squiggles1024/KeyPad/KeyPad_Project/ECAD/B4B-PH-SM4-TB/B4B-PH-SM4-TB.step

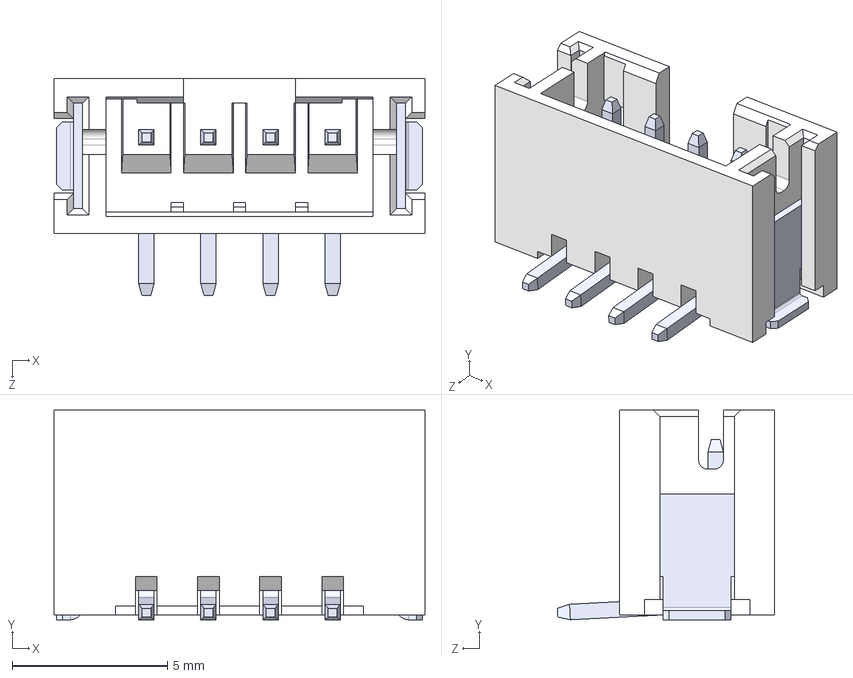
[picture p24: CAD file, 2022-12-01]
KeyPad_Project/ECAD/B4B-PH-SM4-TB/B4B-PH-SM4-TB.step
12.0 x 6.75 x 7.00 mm
