squiggles1024/KeyPad/KeyPad_Project/ECAD/JS5208/JS5208.step

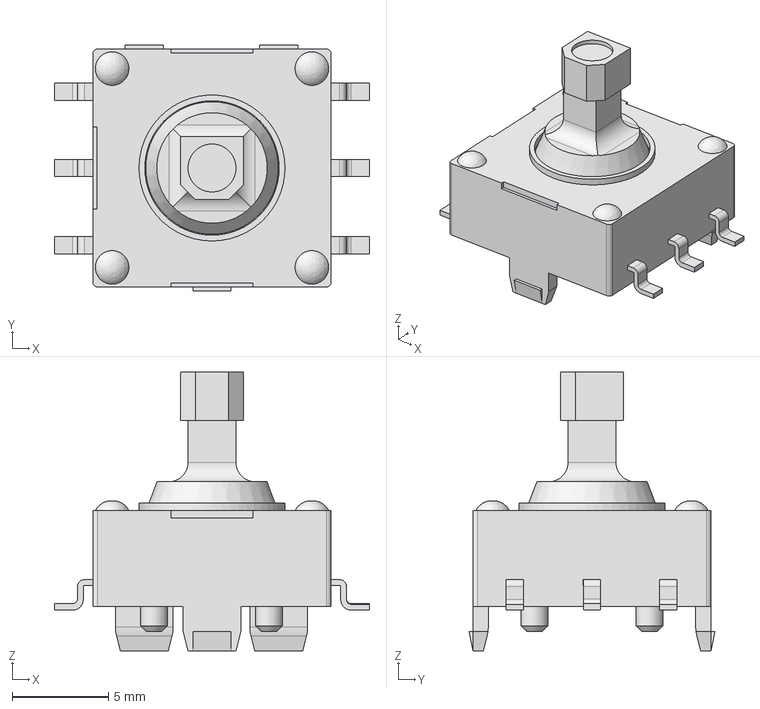
[picture p25: CAD file, 2022-12-01]
KeyPad_Project/ECAD/JS5208/JS5208.step
16.4 x 12.8 x 14.5 mm
