squiggles1024/KeyPad/KeyPad_Project/CAD Parts/12mm-button-without-cap-with-round-square-cap-1.snapshot.3/12mmx12mm With White cap square.stp

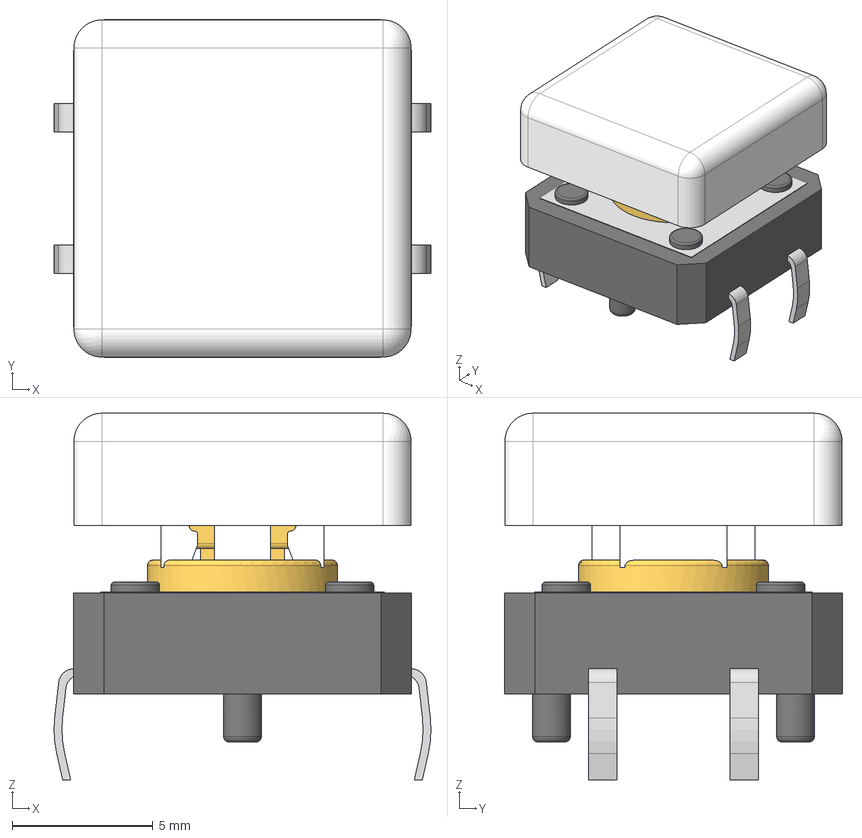
[picture p26: CAD file, 2022-12-01]
KeyPad_Project/CAD Parts/12mm-button-without-cap-with-round-square-cap-1.snapshot.3/12mmx12mm With White cap square.stp
13.4 x 12.0 x 13.0 mm
