squiggles1024/KeyPad/KeyPad_Project/CAD Parts/WheelCover.SLDPRT

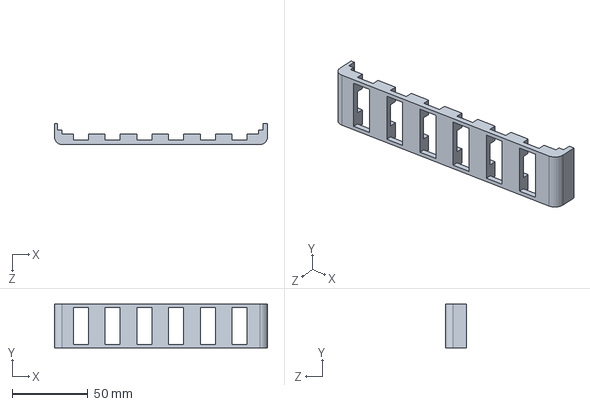
[picture p29: CAD file, 2022-12-01]
KeyPad_Project/CAD Parts/WheelCover.SLDPRT
141.0 x 28.8 x 14.0 mm
