squiggles1024/KeyPad/KeyPad_Project/CAD Parts/d-sub-connector-femaile-1.snapshot.1/femaile/db15.stp

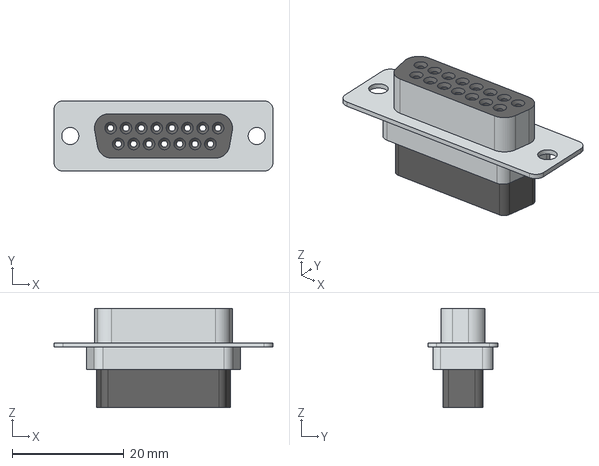
[picture p30: CAD file, 2022-12-01]
KeyPad_Project/CAD Parts/d-sub-connector-femaile-1.snapshot.1/femaile/db15.stp
39.1 x 12.5 x 17.7 mm
