squiggles1024/KeyPad/KeyPad_Project/CAD Parts/tactile-switch-thru-6mm-series-1.snapshot.25/Tactal Switch -Thru (6mmx 6mmx17.0mm).stp

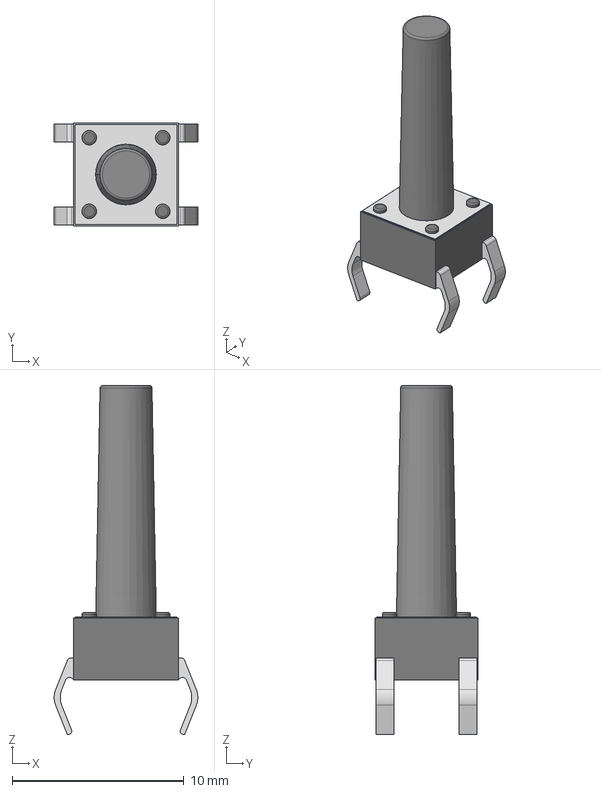
[picture p31: CAD file, 2022-12-01]
KeyPad_Project/CAD Parts/tactile-switch-thru-6mm-series-1.snapshot.25/Tactal Switch -Thru (6mmx 6mmx17.0mm).stp
8.37 x 5.99 x 20.3 mm
