squiggles1024/KeyPad/KeyPad_Project/CAD Parts/BoardCover.SLDPRT

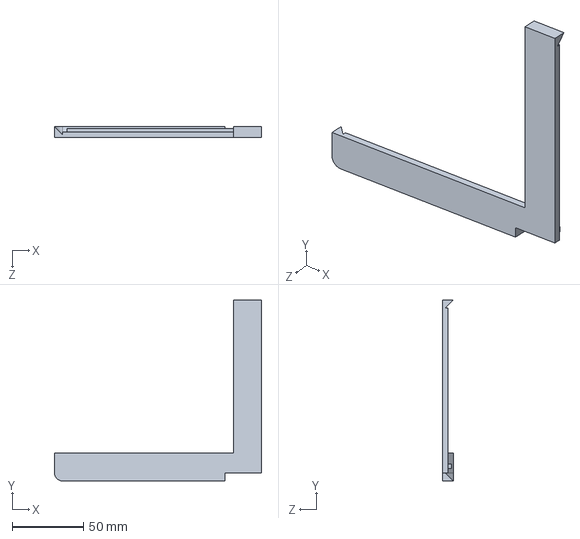
[picture p33: CAD file, 2022-12-01]
KeyPad_Project/CAD Parts/BoardCover.SLDPRT
145.7 x 127.3 x 7.66 mm
