squiggles1024/KeyPad/KeyPad_Project/CAD Parts/ThumbpadBase.SLDPRT

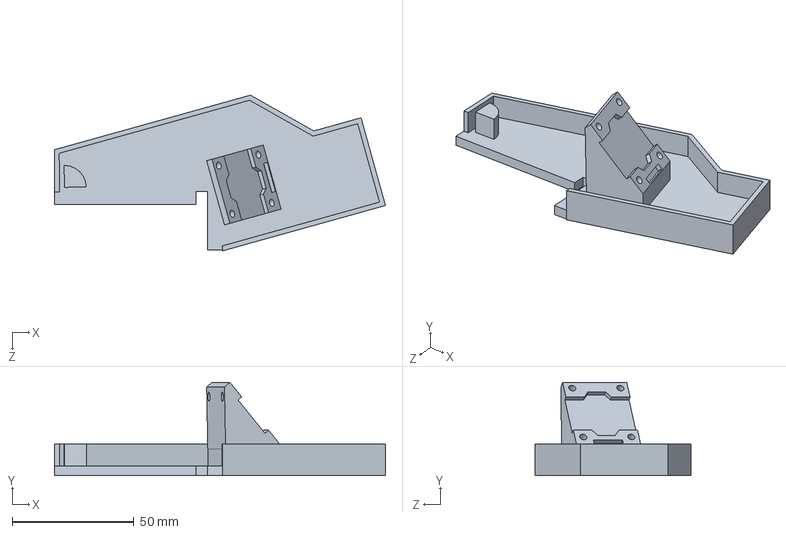
[picture p37: CAD file, 2022-12-01]
KeyPad_Project/CAD Parts/ThumbpadBase.SLDPRT
136.0 x 38.4 x 64.0 mm
