squiggles1024/KeyPad/KeyPad_Project/CAD Parts/tactile-switch-thru-6mm-series-1.snapshot.25/Tactal Switch -Thru (6mmx 6mmx4.5mm).stp

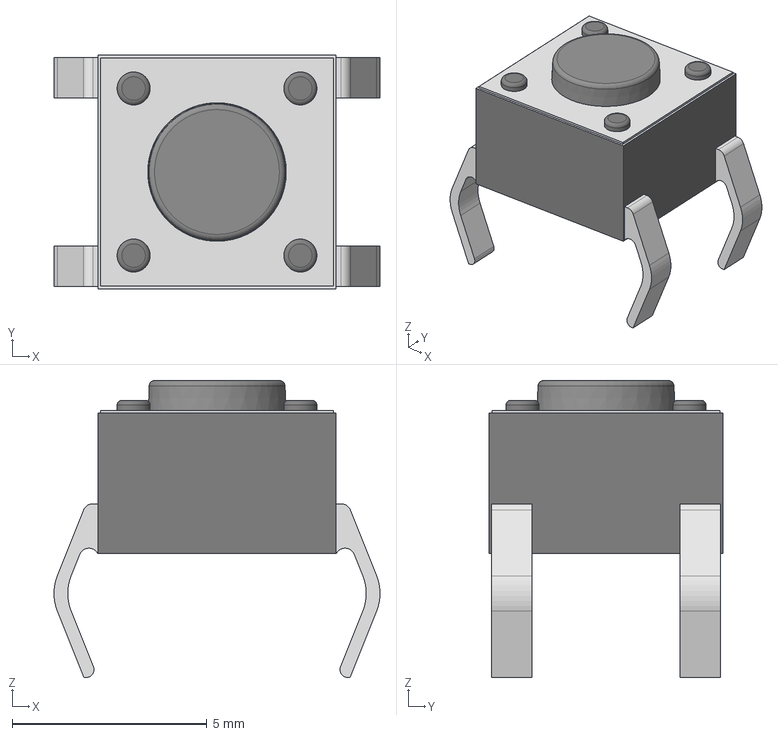
[picture p38: CAD file, 2022-12-01]
KeyPad_Project/CAD Parts/tactile-switch-thru-6mm-series-1.snapshot.25/Tactal Switch -Thru (6mmx 6mmx4.5mm).stp
8.37 x 5.99 x 7.62 mm
