squiggles1024/KeyPad/KeyPad_Project/CAD Parts/Housing.SLDPRT

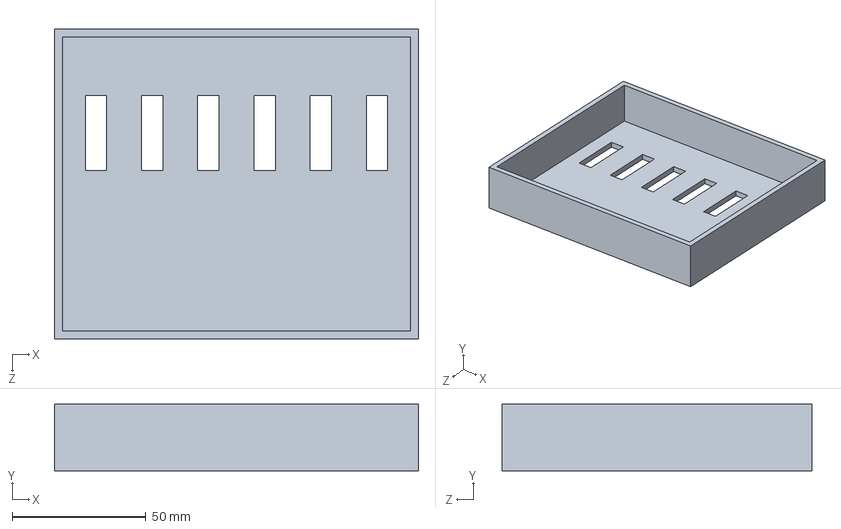
[picture p39: CAD file, 2022-12-01]
KeyPad_Project/CAD Parts/Housing.SLDPRT
136.0 x 25.0 x 116.0 mm
