squiggles1024/KeyPad/KeyPad_Project/CAD Parts/KeypadBase.SLDPRT

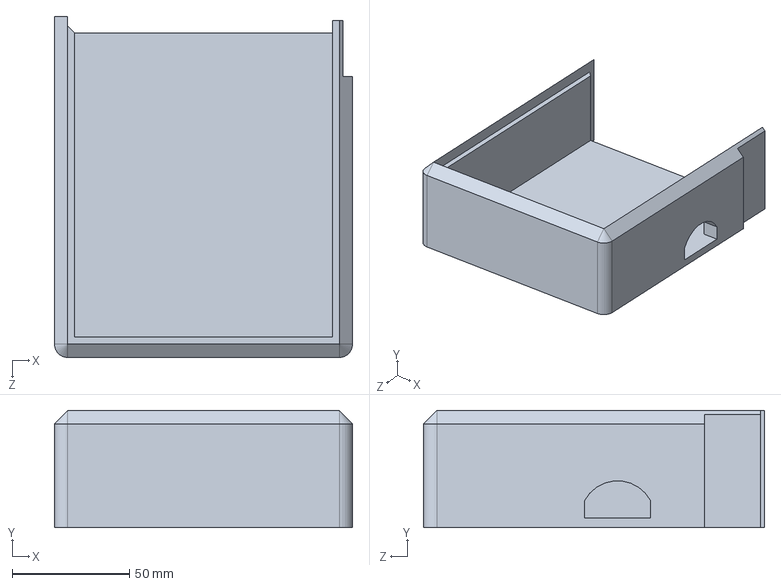
[picture p42: CAD file, 2022-12-01]
KeyPad_Project/CAD Parts/KeypadBase.SLDPRT
127.3 x 50.0 x 145.7 mm
