squiggles1024/KeyPad/KeyPad_Project/CAD Parts/WheelBracket.SLDPRT

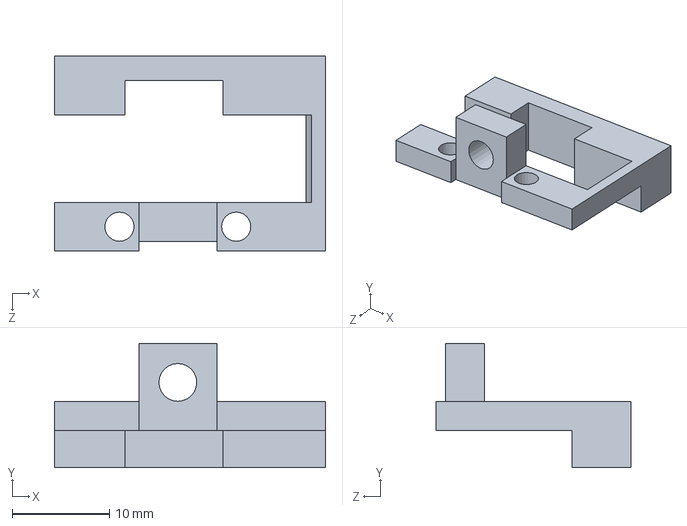
[picture p45: CAD file, 2022-12-01]
KeyPad_Project/CAD Parts/WheelBracket.SLDPRT
27.9 x 12.7 x 20.0 mm
