squiggles1024/KeyPad/KeyPad_Project/CAD Parts/Sensei Scroll Wheel.3MF

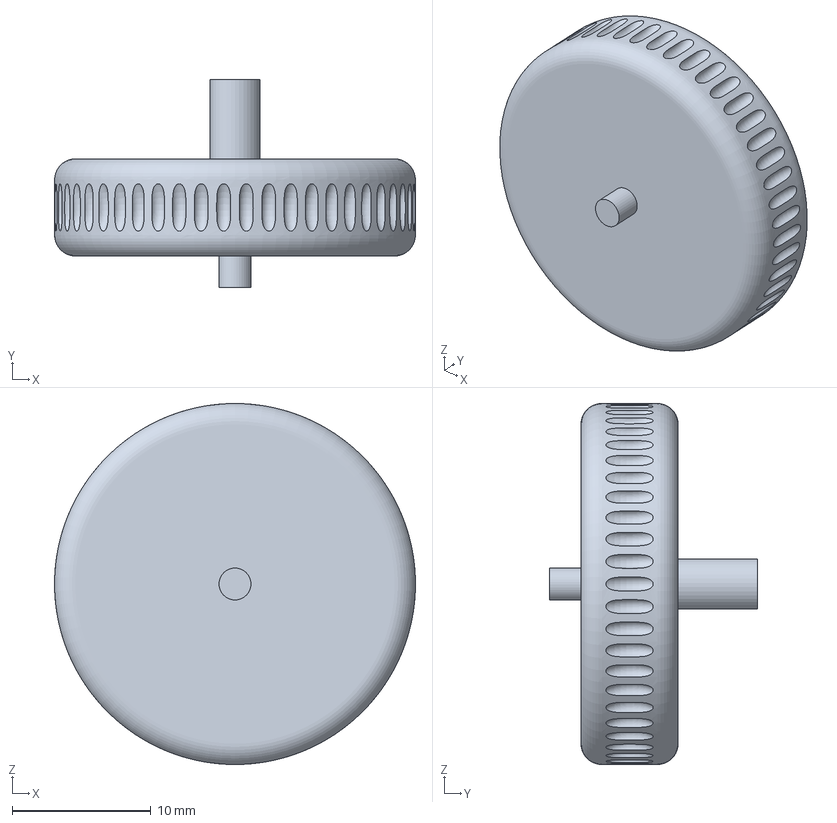
[picture p46: CAD file, 2022-12-01]
KeyPad_Project/CAD Parts/Sensei Scroll Wheel.3MF
26.0 x 14.9 x 26.0 mm
