squiggles1024/KeyPad/KeyPad_Project/CAD Parts/Rim.SLDPRT

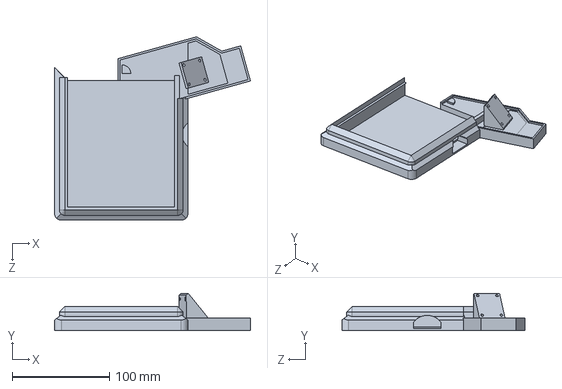
[picture p48: CAD file, 2022-12-01]
KeyPad_Project/CAD Parts/Rim.SLDPRT
201.5 x 38.4 x 188.5 mm
