squiggles1024/KeyPad/KeyPad_Project/CAD Parts/Thumbpad.SLDPRT

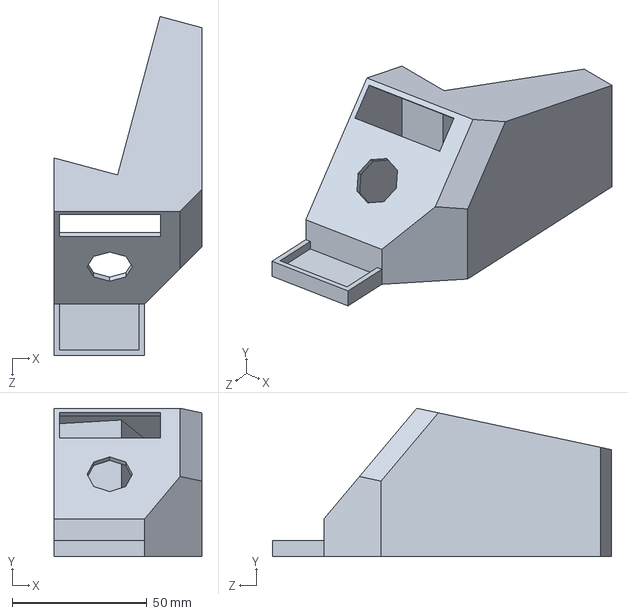
[picture p52: CAD file, 2022-12-01]
KeyPad_Project/CAD Parts/Thumbpad.SLDPRT
54.6 x 55.0 x 125.6 mm
