squiggles1024/KeyPad/KeyPad_Project/CAD Parts/TouchScreenHolder.SLDPRT

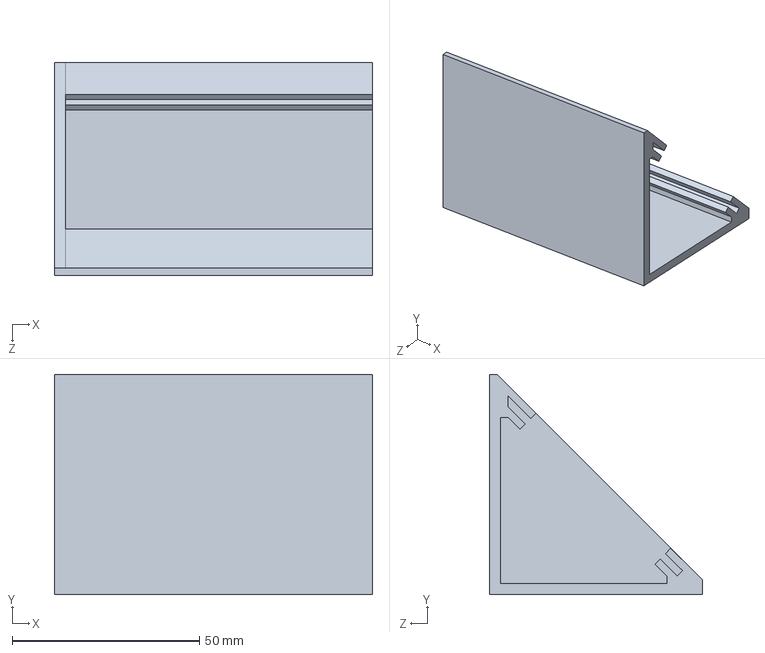
[picture p54: CAD file, 2022-12-01]
KeyPad_Project/CAD Parts/TouchScreenHolder.SLDPRT
85.0 x 58.9 x 57.0 mm
