squiggles1024/KeyPad/KeyPad_Project/CAD Parts/HandRest2.SLDPRT

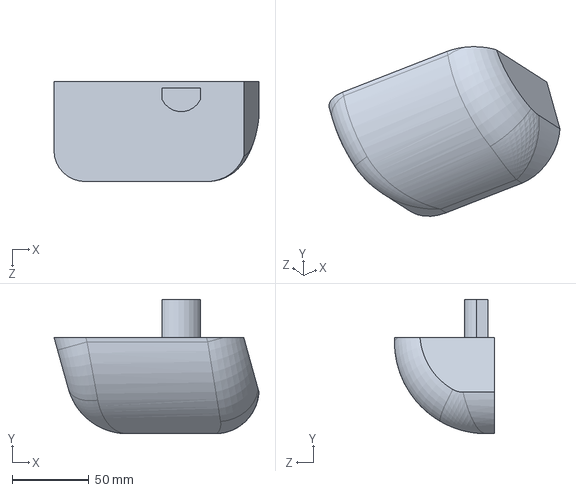
[picture p55: CAD file, 2022-12-01]
KeyPad_Project/CAD Parts/HandRest2.SLDPRT
133.9 x 87.9 x 65.5 mm
