squiggles1024/KeyPad/KeyPad_Project/CAD Parts/KeyCap.SLDPRT

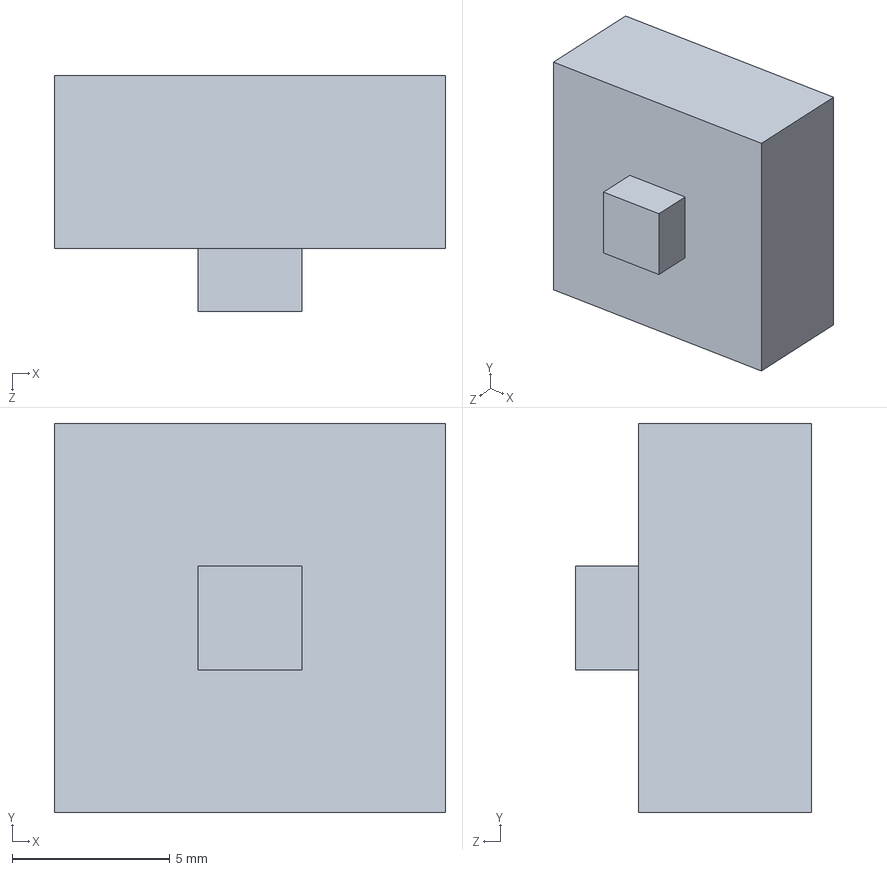
[picture p57: CAD file, 2022-12-01]
KeyPad_Project/CAD Parts/KeyCap.SLDPRT
12.4 x 12.4 x 7.50 mm
