squiggles1024/KeyPad/Core/Inc/main.h

#define ADC_VX_Pin GPIO_PIN_3
#define ADC_VX_GPIO_Port GPIOA
#define ADC_VY_Pin GPIO_PIN_4
#define ADC_VY_GPIO_Port GPIOA
#define SPI1_CSN_Pin GPIO_PIN_0
#define SPI1_CSN_GPIO_Port GPIOB
#define DCRS_Pin GPIO_PIN_1
#define DCRS_GPIO_Port GPIOB
