squiggles1024/KeyPad/Core/Src/i2c.c

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
/* Includes ------------------------------------------------------------------*/
#include "i2c.h"

I2C_HandleTypeDef hi2c1;
I2C_HandleTypeDef hi2c2;
DMA_HandleTypeDef hdma_i2c1_rx;
DMA_HandleTypeDef hdma_i2c2_rx;

/* I2C1 init function */
void MX_I2C1_Init(void)
{

  hi2c1.Instance = I2C1;
  hi2c1.Init.ClockSpeed = 400000;
  hi2c1.Init.DutyCycle = I2C_DUTYCYCLE_2;
  hi2c1.Init.OwnAddress1 = 0;
  hi2c1.Init.AddressingMode = I2C_ADDRESSINGMODE_7BIT;
  hi2c1.Init.DualAddressMode = I2C_DUALADDRESS_DISABLE;
  hi2c1.Init.OwnAddress2 = 0;
  hi2c1.Init.GeneralCallMode = I2C_GENERALCALL_DISABLE;
  hi2c1.Init.NoStretchMode = I2C_NOSTRETCH_DISABLE;
  if (HAL_I2C_Init(&hi2c1) != HAL_OK)
  {
    Error_Handler();
  }
}
/* I2C2 init function */
void MX_I2C2_Init(void)
{

  hi2c2.Instance = I2C2;
  hi2c2.Init.ClockSpeed = 100000;
  hi2c2.Init.DutyCycle = I2C_DUTYCYCLE_2;
  hi2c2.Init.OwnAddress1 = 0;
  hi2c2.Init.AddressingMode = I2C_ADDRESSINGMODE_7BIT;
  hi2c2.Init.DualAddressMode = I2C_DUALADDRESS_DISABLE;
  hi2c2.Init.OwnAddress2 = 0;
  hi2c2.Init.GeneralCallMode = I2C_GENERALCALL_DISABLE;
  hi2c2.Init.NoStretchMode = I2C_NOSTRETCH_DISABLE;
  if (HAL_I2C_Init(&hi2c2) != HAL_OK)
  {
    Error_Handler();
  }
}

void HAL_I2C_MspInit(I2C_HandleTypeDef* i2cHandle)
{

  GPIO_InitTypeDef GPIO_InitStruct = {0};
  if(i2cHandle->Instance==I2C1)
  {
    __HAL_RCC_GPIOB_CLK_ENABLE();
    /**I2C1 GPIO Configuration
    PB6     ------> I2C1_SCL
    PB7     ------> I2C1_SDA
    */
    GPIO_InitStruct.Pin = GPIO_PIN_6|GPIO_PIN_7;
    GPIO_InitStruct.Mode = GPIO_MODE_AF_OD;
    GPIO_InitStruct.Pull = GPIO_PULLUP;
    GPIO_InitStruct.Speed = GPIO_SPEED_FREQ_VERY_HIGH;
    GPIO_InitStruct.Alternate = GPIO_AF4_I2C1;
    HAL_GPIO_Init(GPIOB, &GPIO_InitStruct);

    /* I2C1 clock enable */
    __HAL_RCC_I2C1_CLK_ENABLE();

    /* I2C1 DMA Init */
    /* I2C1_RX Init */
    hdma_i2c1_rx.Instance = DMA1_Stream0;
    hdma_i2c1_rx.Init.Channel = DMA_CHANNEL_1;
    hdma_i2c1_rx.Init.Direction = DMA_PERIPH_TO_MEMORY;
    hdma_i2c1_rx.Init.PeriphInc = DMA_PINC_DISABLE;
    hdma_i2c1_rx.Init.MemInc = DMA_MINC_ENABLE;
    hdma_i2c1_rx.Init.PeriphDataAlignment = DMA_PDATAALIGN_BYTE;
    hdma_i2c1_rx.Init.MemDataAlignment = DMA_MDATAALIGN_BYTE;
    hdma_i2c1_rx.Init.Mode = DMA_NORMAL;
    hdma_i2c1_rx.Init.Priority = DMA_PRIORITY_LOW;
    hdma_i2c1_rx.Init.FIFOMode = DMA_FIFOMODE_DISABLE;
    if (HAL_DMA_Init(&hdma_i2c1_rx) != HAL_OK)
    {
      Error_Handler();
    }

    __HAL_LINKDMA(i2cHandle,hdmarx,hdma_i2c1_rx);

  }
  else if(i2cHandle->Instance==I2C2)
  {
    __HAL_RCC_GPIOB_CLK_ENABLE();
    /**I2C2 GPIO Configuration
    PB10     ------> I2C2_SCL
    PB3     ------> I2C2_SDA
    */
    GPIO_InitStruct.Pin = GPIO_PIN_10;
    GPIO_InitStruct.Mode = GPIO_MODE_AF_OD;
    GPIO_InitStruct.Pull = GPIO_NOPULL;
    GPIO_InitStruct.Speed = GPIO_SPEED_FREQ_VERY_HIGH;
    GPIO_InitStruct.Alternate = GPIO_AF4_I2C2;
    HAL_GPIO_Init(GPIOB, &GPIO_InitStruct);

    GPIO_InitStruct.Pin = GPIO_PIN_3;
    GPIO_InitStruct.Mode = GPIO_MODE_AF_OD;
    GPIO_InitStruct.Pull = GPIO_NOPULL;
    GPIO_InitStruct.Speed = GPIO_SPEED_FREQ_VERY_HIGH;
    GPIO_InitStruct.Alternate = GPIO_AF9_I2C2;
    HAL_GPIO_Init(GPIOB, &GPIO_InitStruct);

    /* I2C2 clock enable */
    __HAL_RCC_I2C2_CLK_ENABLE();

    /* I2C2 DMA Init */
    /* I2C2_RX Init */
    hdma_i2c2_rx.Instance = DMA1_Stream2;
    hdma_i2c2_rx.Init.Channel = DMA_CHANNEL_7;
    hdma_i2c2_rx.Init.Direction = DMA_PERIPH_TO_MEMORY;
    hdma_i2c2_rx.Init.PeriphInc = DMA_PINC_DISABLE;
    hdma_i2c2_rx.Init.MemInc = DMA_MINC_ENABLE;
    hdma_i2c2_rx.Init.PeriphDataAlignment = DMA_PDATAALIGN_BYTE;
    hdma_i2c2_rx.Init.MemDataAlignment = DMA_MDATAALIGN_BYTE;
    hdma_i2c2_rx.Init.Mode = DMA_NORMAL;
    hdma_i2c2_rx.Init.Priority = DMA_PRIORITY_LOW;
    hdma_i2c2_rx.Init.FIFOMode = DMA_FIFOMODE_DISABLE;
    if (HAL_DMA_Init(&hdma_i2c2_rx) != HAL_OK)
    {
      Error_Handler();
    }

    __HAL_LINKDMA(i2cHandle,hdmarx,hdma_i2c2_rx);

  }
}

void HAL_I2C_MspDeInit(I2C_HandleTypeDef* i2cHandle)
{

  if(i2cHandle->Instance==I2C1)
  {
    /* Peripheral clock disable */
    __HAL_RCC_I2C1_CLK_DISABLE();

    /**I2C1 GPIO Configuration
    PB6     ------> I2C1_SCL
    PB7     ------> I2C1_SDA
    */
    HAL_GPIO_DeInit(GPIOB, GPIO_PIN_6);

    HAL_GPIO_DeInit(GPIOB, GPIO_PIN_7);

    /* I2C1 DMA DeInit */
    HAL_DMA_DeInit(i2cHandle->hdmarx);
  }
  else if(i2cHandle->Instance==I2C2)
  {
    /* Peripheral clock disable */
    __HAL_RCC_I2C2_CLK_DISABLE();

    /**I2C2 GPIO Configuration
    PB10     ------> I2C2_SCL
    PB3     ------> I2C2_SDA
    */
    HAL_GPIO_DeInit(GPIOB, GPIO_PIN_10);

    HAL_GPIO_DeInit(GPIOB, GPIO_PIN_3);

    /* I2C2 DMA DeInit */
    HAL_DMA_DeInit(i2cHandle->hdmarx);
  }
}

/* USER CODE BEGIN 1 */
void I2C1_Init(void){

	  hi2c1.Instance = I2C1;
	  hi2c1.Init.ClockSpeed = 400000;
	  hi2c1.Init.DutyCycle = I2C_DUTYCYCLE_2;
	  hi2c1.Init.OwnAddress1 = 0;
	  hi2c1.Init.AddressingMode = I2C_ADDRESSINGMODE_7BIT;
	  hi2c1.Init.DualAddressMode = I2C_DUALADDRESS_DISABLE;
	  hi2c1.Init.OwnAddress2 = 0;
	  hi2c1.Init.GeneralCallMode = I2C_GENERALCALL_DISABLE;
	  hi2c1.Init.NoStretchMode = I2C_NOSTRETCH_DISABLE;
	  if (HAL_I2C_Init(&hi2c1) != HAL_OK)
	  {
	    Error_Handler();
	  }

}

void I2C2_Init(void){
	  hi2c2.Instance = I2C2;
	  hi2c2.Init.ClockSpeed = 100000;
	  hi2c2.Init.DutyCycle = I2C_DUTYCYCLE_2;
	  hi2c2.Init.OwnAddress1 = 0;
	  hi2c2.Init.AddressingMode = I2C_ADDRESSINGMODE_7BIT;
	  hi2c2.Init.DualAddressMode = I2C_DUALADDRESS_DISABLE;
	  hi2c2.Init.OwnAddress2 = 0;
	  hi2c2.Init.GeneralCallMode = I2C_GENERALCALL_DISABLE;
	  hi2c2.Init.NoStretchMode = I2C_NOSTRETCH_DISABLE;
	  if (HAL_I2C_Init(&hi2c2) != HAL_OK)
	  {
	    Error_Handler();
	  }
}
/* USER CODE END 1 */
