squiggles1024/KeyPad/Core/Src/tim.c

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
/* Includes ------------------------------------------------------------------*/
#include "tim.h"

TIM_HandleTypeDef htim3;
DMA_HandleTypeDef hdma_tim3_ch1_trig;

/* TIM3 init function */
void MX_TIM3_Init(void)
{

  TIM_ClockConfigTypeDef sClockSourceConfig = {0};
  TIM_MasterConfigTypeDef sMasterConfig = {0};
  TIM_OC_InitTypeDef sConfigOC = {0};

  htim3.Instance = TIM3;
  htim3.Init.Prescaler = 0;
  htim3.Init.CounterMode = TIM_COUNTERMODE_UP;
  htim3.Init.Period = 168 - 1;
  htim3.Init.ClockDivision = TIM_CLOCKDIVISION_DIV1;
  htim3.Init.AutoReloadPreload = TIM_AUTORELOAD_PRELOAD_ENABLE;
  if (HAL_TIM_Base_Init(&htim3) != HAL_OK)
  {
    Error_Handler();
  }
  sClockSourceConfig.ClockSource = TIM_CLOCKSOURCE_INTERNAL;
  if (HAL_TIM_ConfigClockSource(&htim3, &sClockSourceConfig) != HAL_OK)
  {
    Error_Handler();
  }
  if (HAL_TIM_PWM_Init(&htim3) != HAL_OK)
  {
    Error_Handler();
  }
  sMasterConfig.MasterOutputTrigger = TIM_TRGO_RESET;
  sMasterConfig.MasterSlaveMode = TIM_MASTERSLAVEMODE_DISABLE;
  if (HAL_TIMEx_MasterConfigSynchronization(&htim3, &sMasterConfig) != HAL_OK)
  {
    Error_Handler();
  }
  sConfigOC.OCMode = TIM_OCMODE_PWM1;
  sConfigOC.Pulse = 0;
  sConfigOC.OCPolarity = TIM_OCPOLARITY_HIGH;
  sConfigOC.OCFastMode = TIM_OCFAST_DISABLE;
  if (HAL_TIM_PWM_ConfigChannel(&htim3, &sConfigOC, TIM_CHANNEL_1) != HAL_OK)
  {
    Error_Handler();
  }
  HAL_TIM_MspPostInit(&htim3);

}

void HAL_TIM_Base_MspInit(TIM_HandleTypeDef* tim_baseHandle)
{

  if(tim_baseHandle->Instance==TIM3)
  {
    /* TIM3 clock enable */
    __HAL_RCC_TIM3_CLK_ENABLE();

    /* TIM3 DMA Init */
    /* TIM3_CH1_TRIG Init */
    hdma_tim3_ch1_trig.Instance = DMA1_Stream4;
    hdma_tim3_ch1_trig.Init.Channel = DMA_CHANNEL_5;
    hdma_tim3_ch1_trig.Init.Direction = DMA_MEMORY_TO_PERIPH;
    hdma_tim3_ch1_trig.Init.PeriphInc = DMA_PINC_DISABLE;
    hdma_tim3_ch1_trig.Init.MemInc = DMA_MINC_ENABLE;
    hdma_tim3_ch1_trig.Init.PeriphDataAlignment = DMA_PDATAALIGN_HALFWORD;
    hdma_tim3_ch1_trig.Init.MemDataAlignment = DMA_MDATAALIGN_HALFWORD;
    hdma_tim3_ch1_trig.Init.Mode = DMA_CIRCULAR;
    hdma_tim3_ch1_trig.Init.Priority = DMA_PRIORITY_LOW;
    hdma_tim3_ch1_trig.Init.FIFOMode = DMA_FIFOMODE_DISABLE;
    if (HAL_DMA_Init(&hdma_tim3_ch1_trig) != HAL_OK)
    {
      Error_Handler();
    }

    /* Several peripheral DMA handle pointers point to the same DMA handle.
     Be aware that there is only one stream to perform all the requested DMAs. */
    __HAL_LINKDMA(tim_baseHandle,hdma[TIM_DMA_ID_CC1],hdma_tim3_ch1_trig);
    __HAL_LINKDMA(tim_baseHandle,hdma[TIM_DMA_ID_TRIGGER],hdma_tim3_ch1_trig);

  }
}
void HAL_TIM_MspPostInit(TIM_HandleTypeDef* timHandle)
{

  GPIO_InitTypeDef GPIO_InitStruct = {0};
  if(timHandle->Instance==TIM3)
  {
    __HAL_RCC_GPIOB_CLK_ENABLE();
    /**TIM3 GPIO Configuration
    PB4     ------> TIM3_CH1
    */
    GPIO_InitStruct.Pin = GPIO_PIN_4;
    GPIO_InitStruct.Mode = GPIO_MODE_AF_PP;
    GPIO_InitStruct.Pull = GPIO_NOPULL;
    GPIO_InitStruct.Speed = GPIO_SPEED_FREQ_VERY_HIGH;
    GPIO_InitStruct.Alternate = GPIO_AF2_TIM3;
    HAL_GPIO_Init(GPIOB, &GPIO_InitStruct);

  }

}

void HAL_TIM_Base_MspDeInit(TIM_HandleTypeDef* tim_baseHandle)
{

  if(tim_baseHandle->Instance==TIM3)
  {
    /* Peripheral clock disable */
    __HAL_RCC_TIM3_CLK_DISABLE();

    /* TIM3 DMA DeInit */
    HAL_DMA_DeInit(tim_baseHandle->hdma[TIM_DMA_ID_CC1]);
    HAL_DMA_DeInit(tim_baseHandle->hdma[TIM_DMA_ID_TRIGGER]);
  }
}

/* USER CODE BEGIN 1 */
void TIM3_Init(void){

	  TIM_ClockConfigTypeDef sClockSourceConfig = {0};
	  TIM_MasterConfigTypeDef sMasterConfig = {0};
	  TIM_OC_InitTypeDef sConfigOC = {0};


	  htim3.Instance = TIM3;
	  htim3.Init.Prescaler = 0;
	  htim3.Init.CounterMode = TIM_COUNTERMODE_UP;
	  htim3.Init.Period = 120 - 1;
	  htim3.Init.ClockDivision = TIM_CLOCKDIVISION_DIV1;
	  htim3.Init.AutoReloadPreload = TIM_AUTORELOAD_PRELOAD_DISABLE;
	  if (HAL_TIM_Base_Init(&htim3) != HAL_OK)
	  {
	    Error_Handler();
	  }
	  sClockSourceConfig.ClockSource = TIM_CLOCKSOURCE_INTERNAL;
	  if (HAL_TIM_ConfigClockSource(&htim3, &sClockSourceConfig) != HAL_OK)
	  {
	    Error_Handler();
	  }
	  if (HAL_TIM_PWM_Init(&htim3) != HAL_OK)
	  {
	    Error_Handler();
	  }
	  sMasterConfig.MasterOutputTrigger = TIM_TRGO_RESET;
	  sMasterConfig.MasterSlaveMode = TIM_MASTERSLAVEMODE_DISABLE;
	  if (HAL_TIMEx_MasterConfigSynchronization(&htim3, &sMasterConfig) != HAL_OK)
	  {
	    Error_Handler();
	  }
	  sConfigOC.OCMode = TIM_OCMODE_PWM1;
	  sConfigOC.Pulse = 0;
	  sConfigOC.OCPolarity = TIM_OCPOLARITY_HIGH;
	  sConfigOC.OCFastMode = TIM_OCFAST_DISABLE;
	  if (HAL_TIM_PWM_ConfigChannel(&htim3, &sConfigOC, TIM_CHANNEL_1) != HAL_OK)
	  {
	    Error_Handler();
	  }

	  HAL_TIM_MspPostInit(&htim3);
}

void TIM3_Init2(){

	  TIM_ClockConfigTypeDef sClockSourceConfig = {0};
	  TIM_MasterConfigTypeDef sMasterConfig = {0};
	  TIM_OC_InitTypeDef sConfigOC = {0};

	  htim3.Instance = TIM3;
	  htim3.Init.Prescaler = 0;
	  htim3.Init.CounterMode = TIM_COUNTERMODE_UP;
	  htim3.Init.Period = 168 - 1;
	  htim3.Init.ClockDivision = TIM_CLOCKDIVISION_DIV1;
	  htim3.Init.AutoReloadPreload = TIM_AUTORELOAD_PRELOAD_ENABLE;
	  if (HAL_TIM_Base_Init(&htim3) != HAL_OK)
	  {
	    Error_Handler();
	  }
	  sClockSourceConfig.ClockSource = TIM_CLOCKSOURCE_INTERNAL;
	  if (HAL_TIM_ConfigClockSource(&htim3, &sClockSourceConfig) != HAL_OK)
	  {
	    Error_Handler();
	  }
	  if (HAL_TIM_PWM_Init(&htim3) != HAL_OK)
	  {
	    Error_Handler();
	  }
	  sMasterConfig.MasterOutputTrigger = TIM_TRGO_RESET;
	  sMasterConfig.MasterSlaveMode = TIM_MASTERSLAVEMODE_DISABLE;
	  if (HAL_TIMEx_MasterConfigSynchronization(&htim3, &sMasterConfig) != HAL_OK)
	  {
	    Error_Handler();
	  }
	  sConfigOC.OCMode = TIM_OCMODE_PWM1;
	  sConfigOC.Pulse = 0;
	  sConfigOC.OCPolarity = TIM_OCPOLARITY_HIGH;
	  sConfigOC.OCFastMode = TIM_OCFAST_DISABLE;
	  if (HAL_TIM_PWM_ConfigChannel(&htim3, &sConfigOC, TIM_CHANNEL_1) != HAL_OK)
	  {
	    Error_Handler();
	  }
	  HAL_TIM_MspPostInit(&htim3);

}
/* USER CODE END 1 */
