squiggles1024/KeyPad/Core/Src/adc.c

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
/* Includes ------------------------------------------------------------------*/
#include "adc.h"

ADC_HandleTypeDef hadc1;
DMA_HandleTypeDef hdma_adc1;

/* ADC1 init function */
void MX_ADC1_Init(void)
{

  ADC_ChannelConfTypeDef sConfig = {0};

  /** Configure the global features of the ADC (Clock, Resolution, Data Alignment and number of conversion)
  */
  hadc1.Instance = ADC1;
  hadc1.Init.ClockPrescaler = ADC_CLOCK_SYNC_PCLK_DIV4;
  hadc1.Init.Resolution = ADC_RESOLUTION_12B;
  hadc1.Init.ScanConvMode = ENABLE;
  hadc1.Init.ContinuousConvMode = ENABLE;
  hadc1.Init.DiscontinuousConvMode = DISABLE;
  hadc1.Init.ExternalTrigConvEdge = ADC_EXTERNALTRIGCONVEDGE_NONE;
  hadc1.Init.ExternalTrigConv = ADC_SOFTWARE_START;
  hadc1.Init.DataAlign = ADC_DATAALIGN_RIGHT;
  hadc1.Init.NbrOfConversion = 2;
  hadc1.Init.DMAContinuousRequests = ENABLE;
  hadc1.Init.EOCSelection = ADC_EOC_SEQ_CONV;
  if (HAL_ADC_Init(&hadc1) != HAL_OK)
  {
    Error_Handler();
  }

  /** Configure for the selected ADC regular channel its corresponding rank in the sequencer and its sample time.
  */
  sConfig.Channel = ADC_CHANNEL_3;
  sConfig.Rank = 1;
  sConfig.SamplingTime = ADC_SAMPLETIME_480CYCLES;
  if (HAL_ADC_ConfigChannel(&hadc1, &sConfig) != HAL_OK)
  {
    Error_Handler();
  }

  /** Configure for the selected ADC regular channel its corresponding rank in the sequencer and its sample time.
  */
  sConfig.Channel = ADC_CHANNEL_4;
  sConfig.Rank = 2;
  if (HAL_ADC_ConfigChannel(&hadc1, &sConfig) != HAL_OK)
  {
    Error_Handler();
  }
}

void HAL_ADC_MspInit(ADC_HandleTypeDef* adcHandle)
{

  GPIO_InitTypeDef GPIO_InitStruct = {0};
  if(adcHandle->Instance==ADC1)
  {
    /* ADC1 clock enable */
    __HAL_RCC_ADC1_CLK_ENABLE();

    __HAL_RCC_GPIOA_CLK_ENABLE();
    /**ADC1 GPIO Configuration
    PA3     ------> ADC1_IN3
    PA4     ------> ADC1_IN4
    */
    GPIO_InitStruct.Pin = ADC_VX_Pin|ADC_VY_Pin;
    GPIO_InitStruct.Mode = GPIO_MODE_ANALOG;
    GPIO_InitStruct.Pull = GPIO_NOPULL;
    HAL_GPIO_Init(GPIOA, &GPIO_InitStruct);

    /* ADC1 DMA Init */
    /* ADC1 Init */
    hdma_adc1.Instance = DMA2_Stream0;
    hdma_adc1.Init.Channel = DMA_CHANNEL_0;
    hdma_adc1.Init.Direction = DMA_PERIPH_TO_MEMORY;
    hdma_adc1.Init.PeriphInc = DMA_PINC_DISABLE;
    hdma_adc1.Init.MemInc = DMA_MINC_ENABLE;
    hdma_adc1.Init.PeriphDataAlignment = DMA_PDATAALIGN_HALFWORD;
    hdma_adc1.Init.MemDataAlignment = DMA_MDATAALIGN_HALFWORD;
    hdma_adc1.Init.Mode = DMA_CIRCULAR;
    hdma_adc1.Init.Priority = DMA_PRIORITY_LOW;
    hdma_adc1.Init.FIFOMode = DMA_FIFOMODE_DISABLE;
    if (HAL_DMA_Init(&hdma_adc1) != HAL_OK)
    {
      Error_Handler();
    }

    __HAL_LINKDMA(adcHandle,DMA_Handle,hdma_adc1);

  }
}

void HAL_ADC_MspDeInit(ADC_HandleTypeDef* adcHandle)
{

  if(adcHandle->Instance==ADC1)
  {
    /* Peripheral clock disable */
    __HAL_RCC_ADC1_CLK_DISABLE();

    /**ADC1 GPIO Configuration
    PA3     ------> ADC1_IN3
    PA4     ------> ADC1_IN4
    */
    HAL_GPIO_DeInit(GPIOA, ADC_VX_Pin|ADC_VY_Pin);

    /* ADC1 DMA DeInit */
    HAL_DMA_DeInit(adcHandle->DMA_Handle);
  }
}

/* USER CODE BEGIN 1 */
void ADC1_Init(void){
	  ADC_ChannelConfTypeDef sConfig = {0};


	  hadc1.Instance = ADC1;
	  hadc1.Init.ClockPrescaler = ADC_CLOCK_SYNC_PCLK_DIV4;
	  hadc1.Init.Resolution = ADC_RESOLUTION_12B;
	  hadc1.Init.ScanConvMode = ENABLE;
	  hadc1.Init.ContinuousConvMode = ENABLE;
	  hadc1.Init.DiscontinuousConvMode = DISABLE;
	  hadc1.Init.ExternalTrigConvEdge = ADC_EXTERNALTRIGCONVEDGE_NONE;
	  hadc1.Init.ExternalTrigConv = ADC_SOFTWARE_START;
	  hadc1.Init.DataAlign = ADC_DATAALIGN_RIGHT;
	  hadc1.Init.NbrOfConversion = 2;
	  hadc1.Init.DMAContinuousRequests = ENABLE;
	  hadc1.Init.EOCSelection = ADC_EOC_SEQ_CONV;
	  if (HAL_ADC_Init(&hadc1) != HAL_OK)
	  {
	    Error_Handler();
	  }

	  sConfig.Channel = ADC_CHANNEL_3;
	  sConfig.Rank = 1;
	  sConfig.SamplingTime = ADC_SAMPLETIME_480CYCLES;
	  if (HAL_ADC_ConfigChannel(&hadc1, &sConfig) != HAL_OK)
	  {
	    Error_Handler();
	  }

	  sConfig.Channel = ADC_CHANNEL_4;
	  sConfig.Rank = 2;
	  if (HAL_ADC_ConfigChannel(&hadc1, &sConfig) != HAL_OK)
	  {
	    Error_Handler();
	  }

}
/* USER CODE END 1 */
