squiggles1024/KeyPad/Core/Src/dma.c

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

/* Includes ------------------------------------------------------------------*/
#include "dma.h"

/*----------------------------------------------------------------------------*/
/* Configure DMA                                                              */
/*----------------------------------------------------------------------------*/

/**
  * Enable DMA controller clock
  */
void MX_DMA_Init(void)
{

  /* DMA controller clock enable */
  __HAL_RCC_DMA1_CLK_ENABLE();
  __HAL_RCC_DMA2_CLK_ENABLE();

  /* DMA interrupt init */
  /* DMA1_Stream0_IRQn interrupt configuration */
  HAL_NVIC_SetPriority(DMA1_Stream0_IRQn, 2, 0);
  HAL_NVIC_EnableIRQ(DMA1_Stream0_IRQn);
  /* DMA1_Stream2_IRQn interrupt configuration */
  HAL_NVIC_SetPriority(DMA1_Stream2_IRQn, 2, 0);
  HAL_NVIC_EnableIRQ(DMA1_Stream2_IRQn);
  /* DMA1_Stream4_IRQn interrupt configuration */
  HAL_NVIC_SetPriority(DMA1_Stream4_IRQn, 2, 0);
  HAL_NVIC_EnableIRQ(DMA1_Stream4_IRQn);
  /* DMA2_Stream0_IRQn interrupt configuration */
  HAL_NVIC_SetPriority(DMA2_Stream0_IRQn, 2, 0);
  HAL_NVIC_EnableIRQ(DMA2_Stream0_IRQn);

}

/* USER CODE BEGIN 2 */
void I2C1_DMA_Init(void){
	__HAL_RCC_DMA1_CLK_ENABLE();
	HAL_NVIC_SetPriority(DMA1_Stream0_IRQn, 1, 0);
	HAL_NVIC_EnableIRQ(DMA1_Stream0_IRQn);
}
void ADC_DMA_Init(void){
	__HAL_RCC_DMA2_CLK_ENABLE();
	HAL_NVIC_SetPriority(DMA2_Stream0_IRQn, 1, 0);
	//HAL_NVIC_EnableIRQ(DMA2_Stream0_IRQn);
}

void TIM_DMA_Init(void){
	__HAL_RCC_DMA1_CLK_ENABLE();
	HAL_NVIC_SetPriority(DMA1_Stream4_IRQn, 1, 0);
	HAL_NVIC_EnableIRQ(DMA1_Stream4_IRQn);
}

void I2C2_DMA_Init(void){
	__HAL_RCC_DMA1_CLK_ENABLE();
	  HAL_NVIC_SetPriority(DMA1_Stream2_IRQn, 1, 0);
	  HAL_NVIC_EnableIRQ(DMA1_Stream2_IRQn);
}
/* USER CODE END 2 */
